neophenix/drinkmachine/stls/Holes/Tube Channel Curve 3.stl

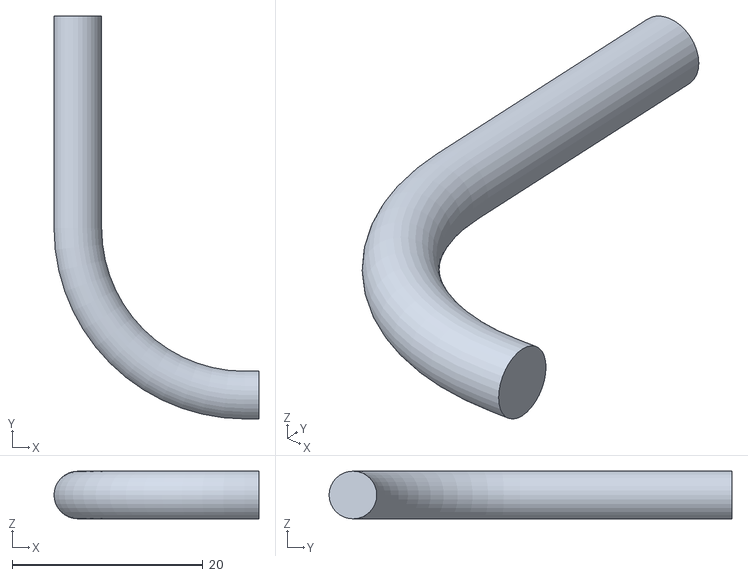
[picture p17: CAD file, 2019-10-15]
stls/Holes/Tube Channel Curve 3.stl
21.5 x 42.2 x 5.00
