neophenix/drinkmachine/stls/Holes/Zip Tie.stl

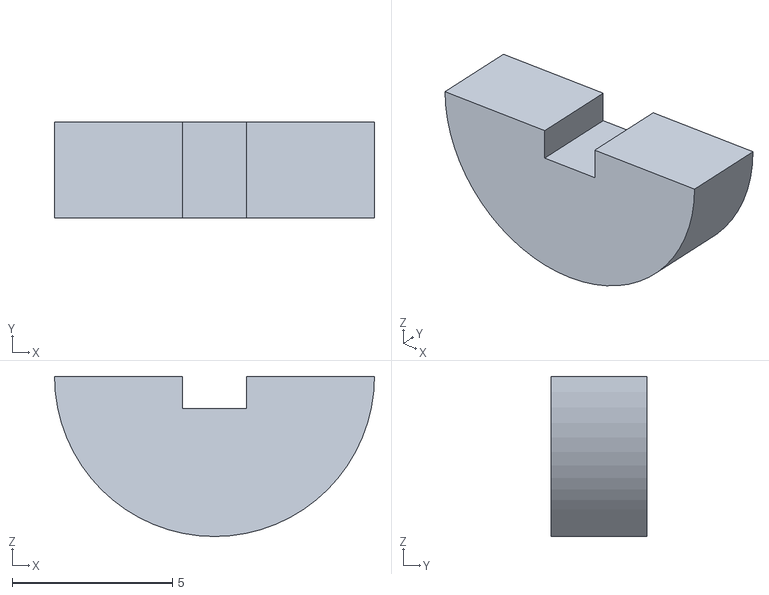
[picture p18: CAD file, 2019-10-15]
stls/Holes/Zip Tie.stl
10.0 x 3.00 x 5.00
