neophenix/drinkmachine/stls/Holes/Tube Channel Curve 1.stl

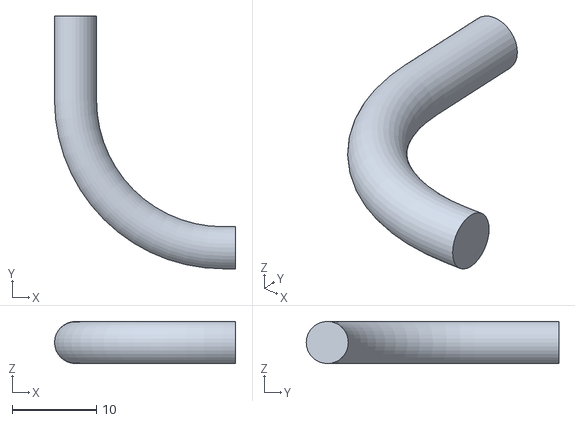
[picture p19: CAD file, 2019-10-15]
stls/Holes/Tube Channel Curve 1.stl
21.5 x 30.0 x 5.00
