neophenix/drinkmachine/stls/Holes/Bottom Clip.stl

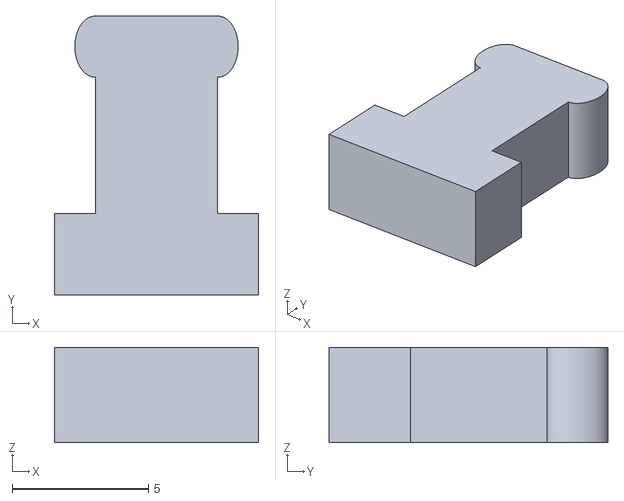
[picture p20: CAD file, 2019-10-15]
stls/Holes/Bottom Clip.stl
7.50 x 10.2 x 3.50
