neophenix/drinkmachine/stls/Holes/Tube Channel Curve 4.stl

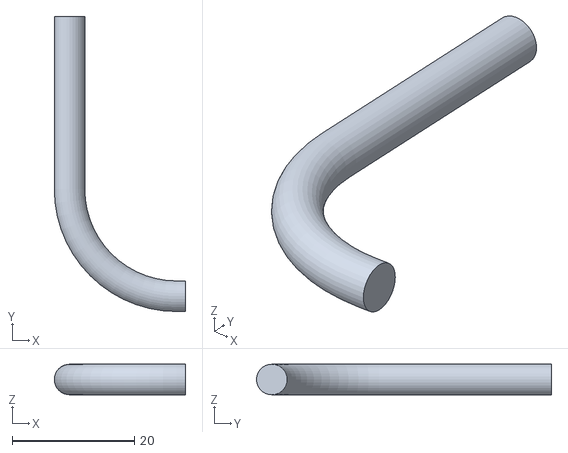
[picture p21: CAD file, 2019-10-15]
stls/Holes/Tube Channel Curve 4.stl
21.5 x 48.2 x 5.00
