neophenix/drinkmachine/stls/Holes/Tube Channel Straight.stl

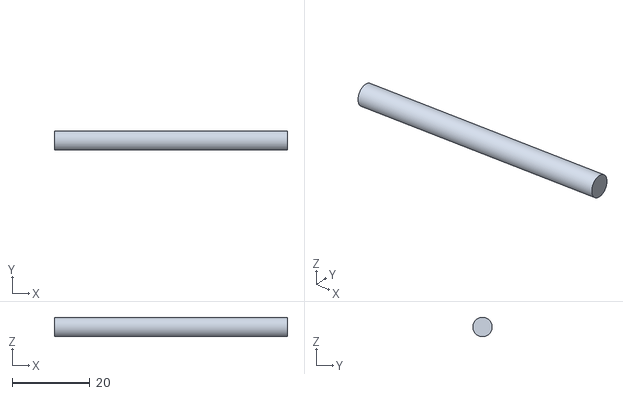
[picture p22: CAD file, 2019-10-15]
stls/Holes/Tube Channel Straight.stl
60.0 x 5.00 x 5.00
