neophenix/drinkmachine/stls/Holes/Pump Mount Plate.stl

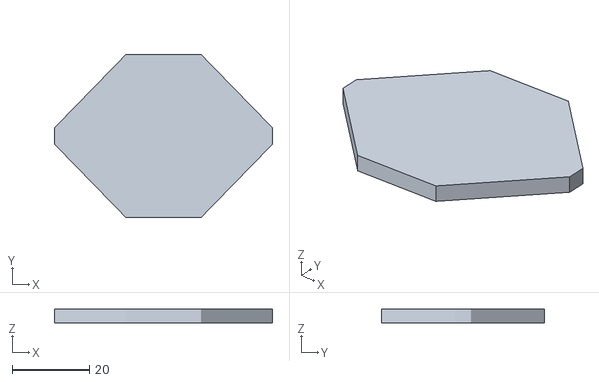
[picture p23: CAD file, 2019-10-15]
stls/Holes/Pump Mount Plate.stl
56.5 x 42.2 x 3.50
