neophenix/drinkmachine/stls/Holes/Cylinder.stl

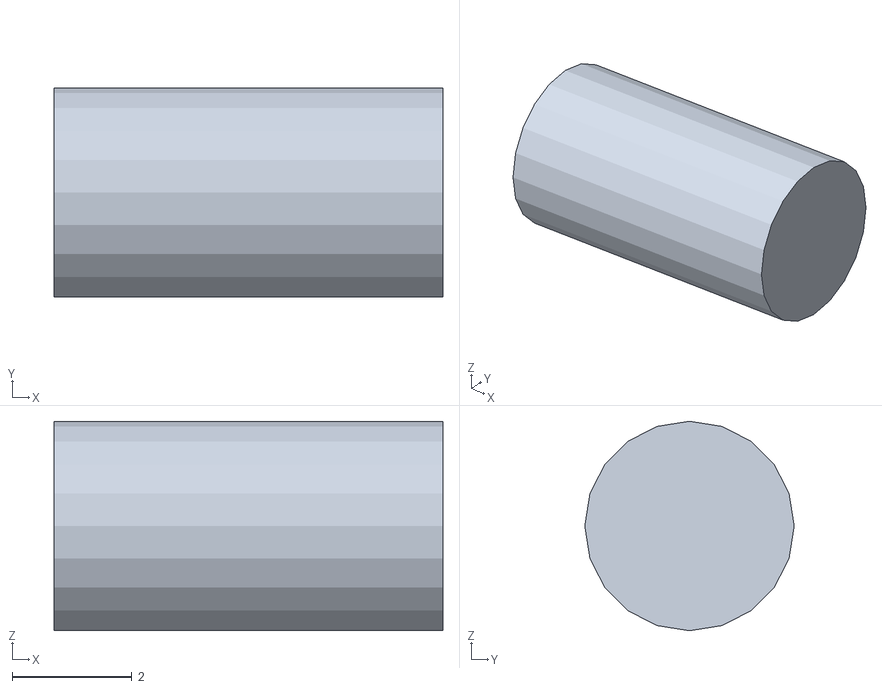
[picture p24: CAD file, 2019-10-15]
stls/Holes/Cylinder.stl
6.50 x 3.50 x 3.50
