neophenix/drinkmachine/stls/Holes/Pump Mount Hole.stl

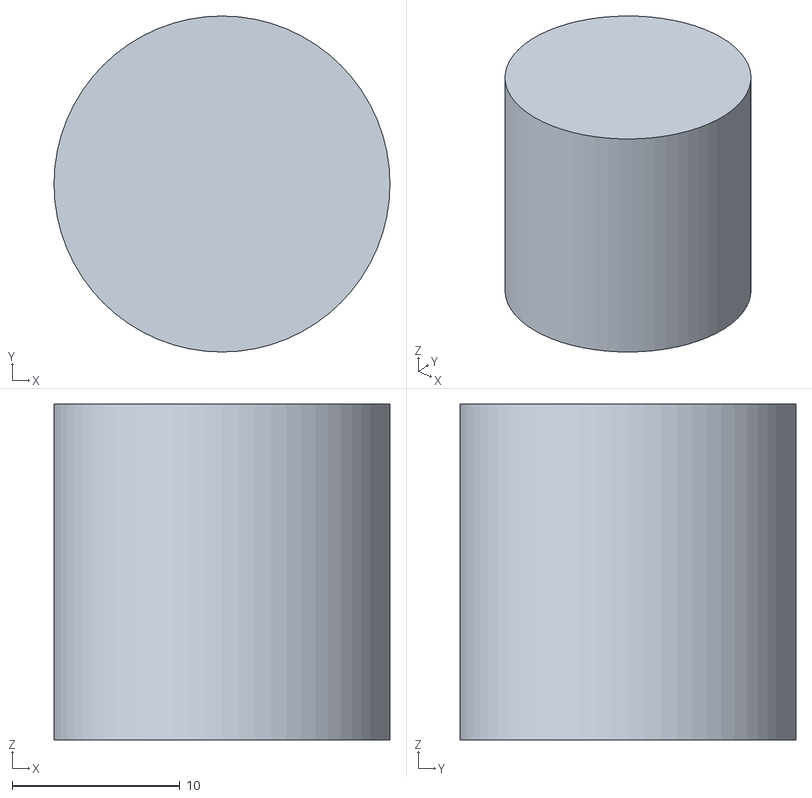
[picture p25: CAD file, 2019-10-15]
stls/Holes/Pump Mount Hole.stl
20.0 x 20.0 x 20.0
