neophenix/drinkmachine/stls/Holes/Nozzle.stl

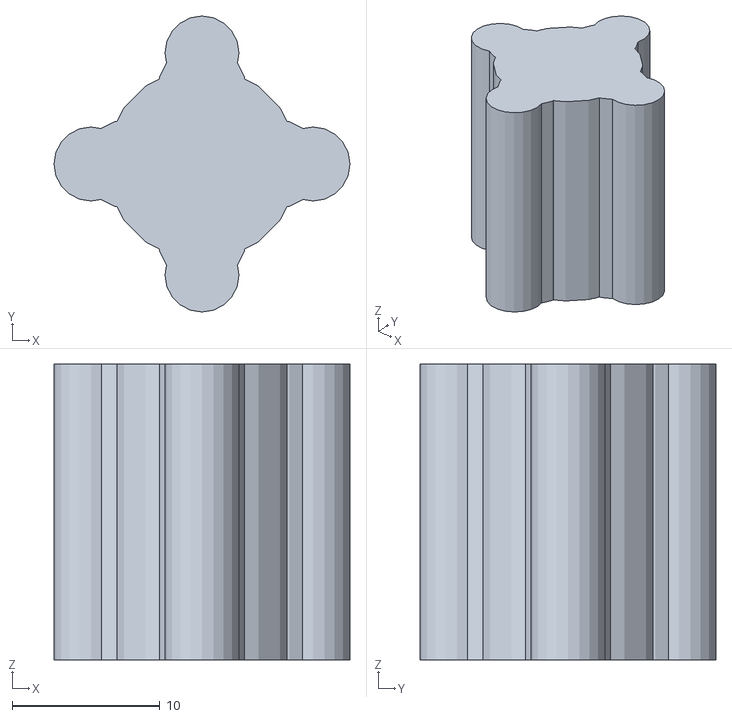
[picture p26: CAD file, 2019-10-15]
stls/Holes/Nozzle.stl
20.0 x 20.0 x 20.0
