neophenix/drinkmachine/stls/Holes/Plug Mount Rear Opening.stl

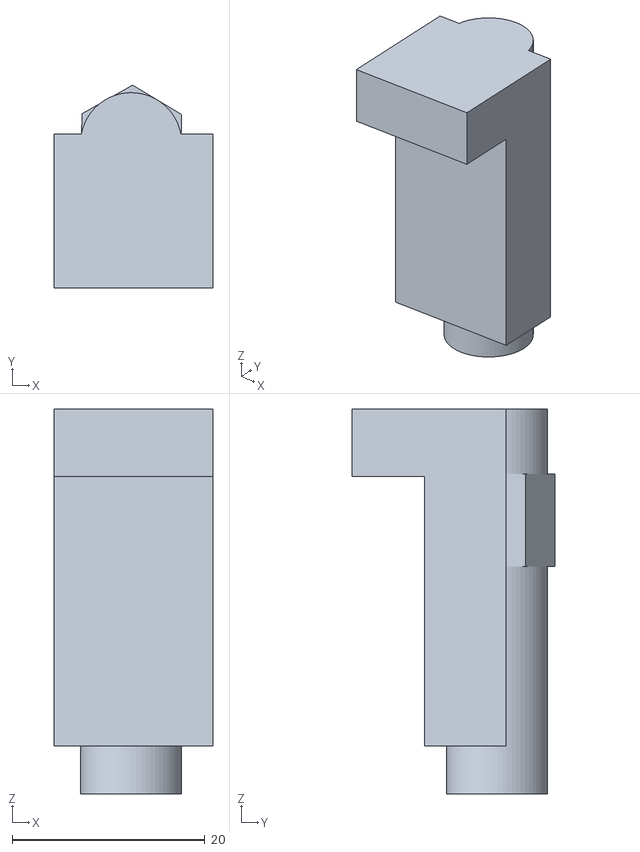
[picture p27: CAD file, 2019-10-15]
stls/Holes/Plug Mount Rear Opening.stl
16.5 x 21.1 x 40.0
