neophenix/drinkmachine/stls/Holes/Tube Channel Front Trim.stl

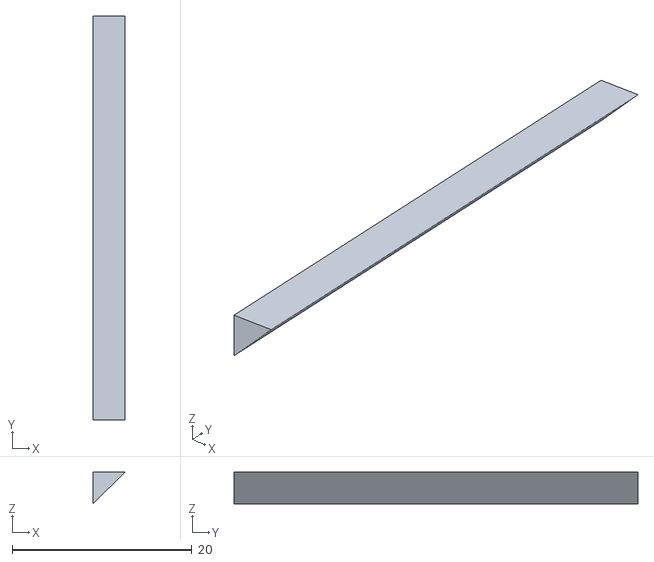
[picture p28: CAD file, 2019-10-15]
stls/Holes/Tube Channel Front Trim.stl
3.54 x 45.0 x 3.54
