neophenix/drinkmachine/stls/Holes/Side T Mount.stl

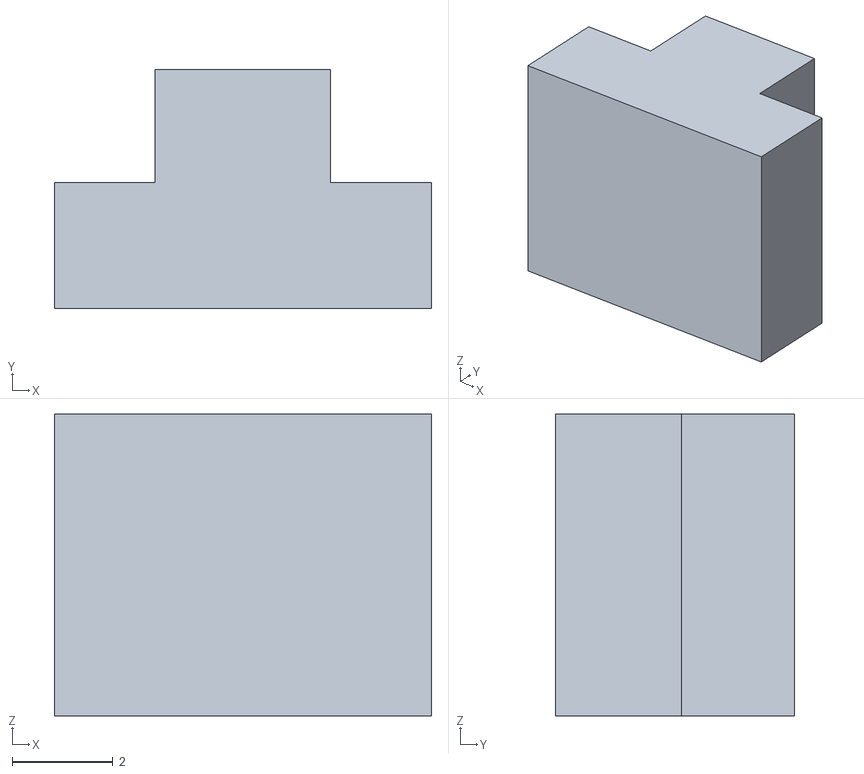
[picture p29: CAD file, 2019-10-15]
stls/Holes/Side T Mount.stl
7.50 x 4.75 x 6.00
