neophenix/drinkmachine/stls/Holes/Tube Channel Curve 2.stl

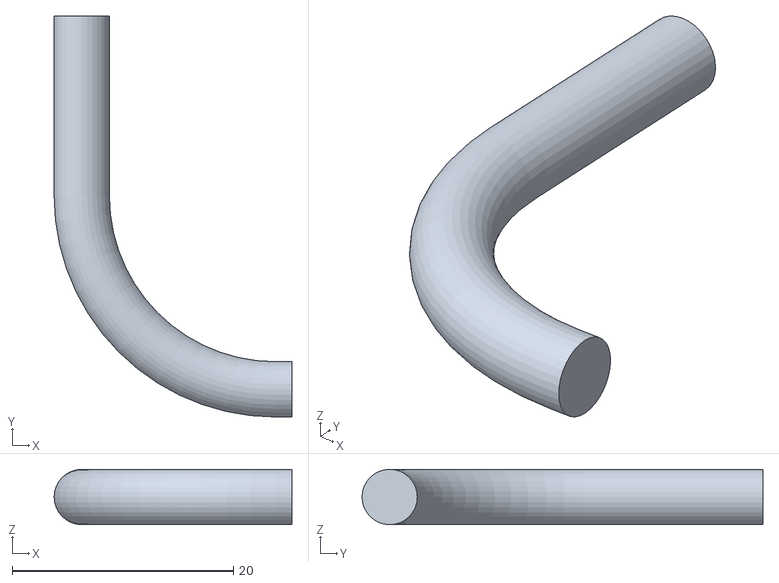
[picture p30: CAD file, 2019-10-15]
stls/Holes/Tube Channel Curve 2.stl
21.5 x 36.2 x 5.00
