neophenix/drinkmachine/stls/Holes/Nozzle Mount.stl

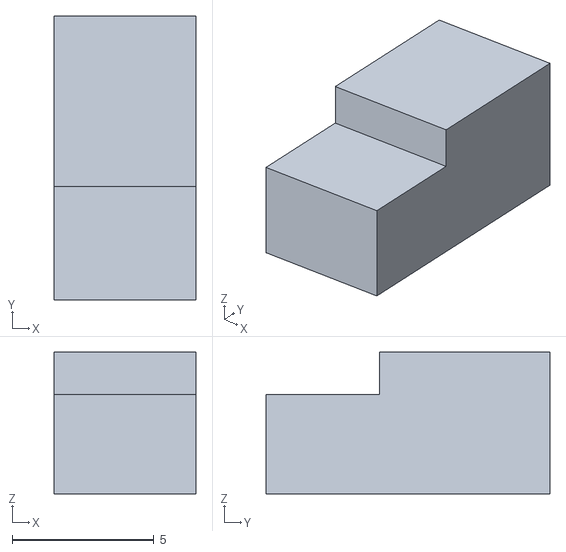
[picture p31: CAD file, 2019-10-15]
stls/Holes/Nozzle Mount.stl
5.00 x 10.0 x 5.00
