neophenix/drinkmachine/stls/Holes/Tube Channel Front.stl

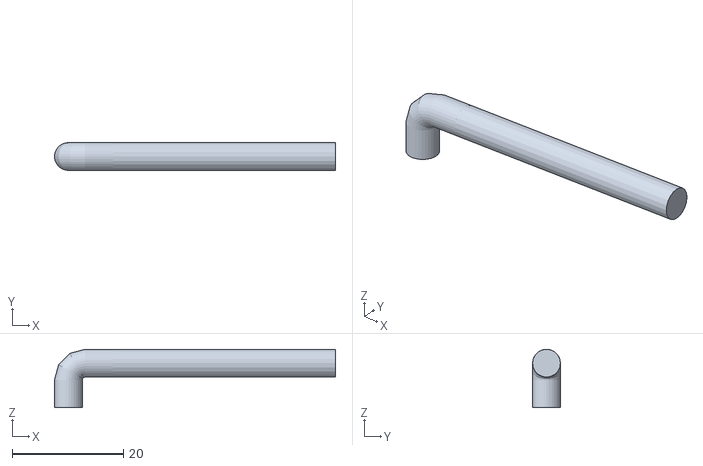
[picture p32: CAD file, 2019-10-15]
stls/Holes/Tube Channel Front.stl
50.5 x 5.00 x 10.5
